Rahix/pavu-mixer/host-daemon/src/pa.rs

#![allow(unused_variables, dead_code)]

use crate::config;
use anyhow::Context;
use pulse::callbacks::ListResult;
use pulse::context;
use pulse::mainloop::standard as mainloop;
use std::cell::Cell;
use std::rc::Rc;
use std::sync::mpsc;

/// Sample Spec for monitoring streams
const SAMPLE_SPEC: pulse::sample::Spec = pulse::sample::Spec {
    format: pulse::sample::Format::FLOAT32NE,
    channels: 1,
    rate: 25,
};

pub struct SinkInputInfo {
    pub index: u32,
    pub name: Option<String>,
    pub application: Option<String>,
    connected_sink: u32,
    pub properties: pulse::proplist::Proplist,
    volume: pulse::volume::ChannelVolumes,
    mute: bool,
}

impl SinkInputInfo {
    fn from_pa(info: &context::introspect::SinkInputInfo) -> Self {
        Self {
            index: info.index,
            name: info.name.as_ref().map(|c| c.to_owned().into_owned()),
            application: info
                .proplist
                .get_str(pulse::proplist::properties::APPLICATION_NAME),
            connected_sink: info.sink,
            properties: info.proplist.clone(),
            volume: info.volume.clone(),
            mute: info.mute,
        }
    }
}

impl std::fmt::Debug for SinkInputInfo {
    fn fmt(&self, f: &mut std::fmt::Formatter<'_>) -> std::fmt::Result {
        let mut propmap = std::collections::BTreeMap::new();
        for key in self.properties.iter() {
            let value = self
                .properties
                .get_str(&key)
                .expect("missing property for iterated key");
            propmap.insert(key, value);
        }
        f.debug_struct("SinkInputInfo")
            .field("index", &self.index)
            .field("name", &self.name)
            .field("application", &self.application)
            .field("connected_sink", &self.connected_sink)
            .field("properties", &propmap)
            .field("volume", &self.volume.avg().print_verbose(true))
            .field("mute", &self.mute)
            .finish()
    }
}

pub struct SinkInfo {
    index: u32,
    name: Option<String>,
    monitoring_source: u32,
    volume: pulse::volume::ChannelVolumes,
    mute: bool,
}

impl SinkInfo {
    fn from_pa(info: &context::introspect::SinkInfo) -> Self {
        Self {
            index: info.index,
            name: info.name.as_ref().map(|c| c.to_owned().into_owned()),
            monitoring_source: info.monitor_source,
            volume: info.volume.clone(),
            mute: info.mute,
        }
    }
}

impl std::fmt::Debug for SinkInfo {
    fn fmt(&self, f: &mut std::fmt::Formatter<'_>) -> std::fmt::Result {
        f.debug_struct("SinkInfo")
            .field("index", &self.index)
            .field("name", &self.name)
            .field("monitoring_source", &self.monitoring_source)
            .field("volume", &self.volume.avg().print_verbose(true))
            .field("mute", &self.mute)
            .finish()
    }
}

#[derive(Debug)]
pub enum Event {
    /// After querying the default sink, PulseAudio came back with this stream.
    NewDefaultSink(Stream),
    /// A new sink-input showed up and we need to check whether it matches any of our channels - if
    /// yes, it should be attached.
    SinkInputAdded(SinkInputInfo),
    /// Some property of a sink-input changed.  It potentially needs to be re-attached to a
    /// different channel.
    SinkInputChanged(SinkInputInfo),
    /// A sink-input was removed and we should probably drop it from a potentially connected
    /// channel as well.
    SinkInputRemoved(u32),
    /// A new sink-input stream is available for the given channel.
    NewSinkInput(common::Channel, Stream),
    /// New signal peak information is available for this stream (sink / sink-input).
    NewPeakData(common::Channel, usize),
    // /// An error occurred asynchronously and we need to abort.
    // FatalError(anyhow::Error),
}

#[derive(Debug)]
enum InternalEvent {
    /// Sinks were added or removed (or default was changed) and we might need to reconnect the
    /// main channel.  This will trigger us to query the default sink next, leading to an external
    /// `DefaultSink` event.
    SinkUpdateNeeded,
    /// PulseAudio reported back the name of the default sink - we can now go and query its
    /// information.
    DefaultSinkName(String),
    /// We got information about the default sink - enough to create a stream for it.
    SinkData(SinkInfo),
    /// A new sink-input was detected - we should query its information and tell the application
    /// about it.
    SinkInputPending(u32),
    /// A sink-input change was detected - we should query its information and tell the application
    /// about the change.
    SinkInputChangePending(u32),
    /// We collected all relevant information for a new sink-input.
    RequestSinkInputStream {
        input_info: SinkInputInfo,
        for_channel: common::Channel,
        monitor_source: u32,
    },
}

/// Interface for interacting with Pulseaudio.
///
/// This interface will provide information about connect{ed,ing} streams, stream peak samples, and
/// allow the mixer to control stream volumes.
///
/// It is built upon the Pulseaudio single-threaded "simple" mainloop.
pub struct PulseInterface {
    mainloop: mainloop::Mainloop,
    pub context: context::Context,
    introspector: context::introspect::Introspector,
    external_rx: Option<mpsc::Receiver<Event>>,
    external_tx: mpsc::Sender<Event>,
    internal_rx: mpsc::Receiver<InternalEvent>,
    internal_tx: mpsc::Sender<InternalEvent>,

    /// Name of the current default sink (used to check if it changed).
    current_default_sink: Option<String>,
}

impl PulseInterface {
    pub fn init() -> anyhow::Result<Self> {
        let mut proplist = pulse::proplist::Proplist::new().context("failed creating proplist")?;
        proplist
            .set_str(
                pulse::proplist::properties::APPLICATION_NAME,
                "Pavu-Mixer Daemon",
            )
            .ok()
            .context("failed setting proplist string")?;

        let mut mainloop = mainloop::Mainloop::new().context("failed creating mainloop")?;
        let mut context =
            pulse::context::Context::new_with_proplist(&mainloop, "PavuMixerContext", &proplist)
                .context("failed creating context")?;
        context
            .connect(None, pulse::context::FlagSet::NOFLAGS, None)
            .context("failed connecting context")?;

        'wait_for_ctx: loop {
            Self::iterate_mainloop(&mut mainloop, true)?;
            match context.get_state() {
                pulse::context::State::Ready => {
                    break 'wait_for_ctx;
                }
                pulse::context::State::Terminated | pulse::context::State::Failed => {
                    anyhow::bail!("terminated or failed context");
                }
                _ => (),
            }
        }

        let introspector = context.introspect();

        let (external_tx, external_rx) = mpsc::channel();
        let (internal_tx, internal_rx) = mpsc::channel();

        context.set_subscribe_callback({
            let external_tx = external_tx.clone();
            let internal_tx = internal_tx.clone();
            Some(Box::new(move |facility, op, index| {
                use pulse::context::subscribe::Facility;
                use pulse::context::subscribe::Operation;

                // it would be very odd if PulseAudio gave us invalid enum values
                let op = op.expect("invalid subscribe callback params");
                let facility = facility.expect("invalid subscribe callback params");

                match (facility, op) {
                    (Facility::Sink, Operation::New) => internal_tx
                        .send(InternalEvent::SinkUpdateNeeded)
                        .expect("event channel error"),
                    (Facility::Sink, Operation::Removed) => internal_tx
                        .send(InternalEvent::SinkUpdateNeeded)
                        .expect("event channel error"),
                    (Facility::Sink, Operation::Changed) => (), // ignore
                    (Facility::Server, _) => internal_tx
                        .send(InternalEvent::SinkUpdateNeeded) // default sink might have changed
                        .expect("event channel error"),
                    (Facility::SinkInput, Operation::New) => internal_tx
                        .send(InternalEvent::SinkInputPending(index))
                        .expect("event channel error"),
                    (Facility::SinkInput, Operation::Removed) => external_tx
                        .send(Event::SinkInputRemoved(index))
                        .expect("event channel error"),
                    (Facility::SinkInput, Operation::Changed) => internal_tx
                        .send(InternalEvent::SinkInputChangePending(index))
                        .expect("event channel error"),
                    _ => unreachable!("unexpected facility: {:?}", facility),
                };
            }))
        });

        // subscribe to interesting events:
        // - SINK: if the available sinks (= output devices) change
        // - SINK_INPUT: if the playing audio sources change
        // - SERVER: if the selected default sink (output device) changes
        {
            use pulse::context::subscribe::InterestMaskSet;
            context.subscribe(
                InterestMaskSet::SINK | InterestMaskSet::SINK_INPUT | InterestMaskSet::SERVER,
                |_| (),
            );
        }

        // Queue initial events to get the mixer going.  This means triggering an update of the
        // default sink...
        internal_tx
            .send(InternalEvent::SinkUpdateNeeded)
            .expect("event channel error");

        // ...and "adding" all currently existing sink-inputs.
        let done = Rc::new(Cell::new(Ok(false)));
        introspector.get_sink_input_info_list({
            let external_tx = external_tx.clone();
            let done = done.clone();
            move |result| match result {
                ListResult::Item(info) => {
                    external_tx
                        .send(Event::SinkInputAdded(SinkInputInfo::from_pa(info)))
                        .expect("event channel error");
                }
                ListResult::Error => done.set(Err(anyhow::anyhow!("pulseaudio list error"))),
                ListResult::End => done.set(Ok(true)),
            }
        });

        let mut this = Self {
            mainloop,
            context,
            introspector,
            external_rx: Some(external_rx),
            external_tx,
            internal_rx,
            internal_tx,

            current_default_sink: None,
        };

        'add_all_sink_inputs: loop {
            this.iterate(true)?;
            // returns `true` once we hit the end of the sink-input list
            if done.replace(Ok(false))? {
                break 'add_all_sink_inputs;
            }
        }

        Ok(this)
    }

    fn iterate_mainloop(mainloop: &mut mainloop::Mainloop, block: bool) -> anyhow::Result<()> {
        match mainloop.iterate(block) {
            mainloop::IterateResult::Success(_) => Ok(()),
            mainloop::IterateResult::Quit(_) => unreachable!("no code should quit the mainloop!"),
            mainloop::IterateResult::Err(e) => Err(e).context("failed mainloop iteration"),
        }
    }

    pub fn take_event_receiver(&mut self) -> Option<mpsc::Receiver<Event>> {
        self.external_rx.take()
    }

    pub fn iterate(&mut self, block: bool) -> anyhow::Result<()> {
        Self::iterate_mainloop(&mut self.mainloop, block)?;
        while let Ok(event) = self.internal_rx.try_recv() {
            match event {
                InternalEvent::SinkUpdateNeeded => self.query_default_sink(),
                InternalEvent::DefaultSinkName(name) => {
                    if self.current_default_sink.as_ref() != Some(&name) {
                        // the name differs from the previous one - we need to issue an update
                        self.query_sink_data(&name);
                    }
                }
                InternalEvent::SinkData(info) => {
                    // Create a new stream and pass it to the application
                    let stream = Stream::new_for_sink(self, info)
                        .context("failed creating monitoring stream for default sink")?;
                    self.external_tx
                        .send(Event::NewDefaultSink(stream))
                        .expect("event channel error");
                }
                InternalEvent::SinkInputPending(index) => self.query_added_sink_input(index),
                InternalEvent::SinkInputChangePending(index) => {
                    self.query_changed_sink_input(index)
                }
                InternalEvent::RequestSinkInputStream {
                    input_info,
                    for_channel,
                    monitor_source,
                } => {
                    let stream = Stream::new_for_sink_input(self, input_info, monitor_source)?;
                    self.external_tx
                        .send(Event::NewSinkInput(for_channel, stream))
                        .expect("event channel error");
                }
            }
        }
        Ok(())
    }

    /// Request a stream for a sink-input.
    ///
    /// This will first query the sink-input's sink to get its monitoring source.
    ///
    /// Once received, the stream will be pushed as an event.
    pub fn request_sink_input_stream(
        &mut self,
        input_info: SinkInputInfo,
        for_channel: common::Channel,
    ) {
        let connected_sink = input_info.connected_sink;
        let mut input_info = Some(input_info);
        self.introspector.get_sink_info_by_index(connected_sink, {
            let internal_tx = self.internal_tx.clone();
            move |result| match result {
                ListResult::Item(info) => {
                    internal_tx
                        .send(InternalEvent::RequestSinkInputStream {
                            input_info: input_info.take().expect(
                                "callback for request_sink_input_stream() called too often",
                            ),
                            for_channel,
                            monitor_source: info.monitor_source,
                        })
                        .expect("event channel error");
                }
                ListResult::End => (),
                ListResult::Error => {
                    log::warn!("error while querying sink data - ignoring this sink")
                }
            }
        });
    }

    /// Query the default sink.
    ///
    /// Triggers [`InternalEvent::DefaultSinkName`] on completion.
    fn query_default_sink(&mut self) {
        self.introspector.get_server_info({
            let internal_tx = self.internal_tx.clone();
            move |info| {
                if let Some(default_sink) = &info.default_sink_name {
                    internal_tx.send(InternalEvent::DefaultSinkName(default_sink.clone().into_owned())).expect("event channel error");
                } else {
                    log::warn!("PulseAudio does not have a default sink - the main channel is not operational.");
                }
            }
        });
    }

    /// Query sink information for a sink.
    ///
    /// Triggers [`InternalEvent::SinkData`] on completion.
    fn query_sink_data(&mut self, sink_name: &str) {
        self.introspector.get_sink_info_by_name(sink_name, {
            let internal_tx = self.internal_tx.clone();
            move |result| match result {
                ListResult::Item(info) => {
                    internal_tx
                        .send(InternalEvent::SinkData(SinkInfo::from_pa(info)))
                        .expect("event channel error");
                }
                ListResult::End => (),
                ListResult::Error => {
                    log::warn!("error while querying sink data - ignoring this sink")
                }
            }
        });
    }

    /// Query a newly added sink-input.
    ///
    /// Triggers [`Event::SinkInputAdded`] on completion.
    fn query_added_sink_input(&mut self, index: u32) {
        self.introspector.get_sink_input_info(index, {
            let external_tx = self.external_tx.clone();
            move |result| match result {
                ListResult::Item(info) => {
                    external_tx
                        .send(Event::SinkInputAdded(SinkInputInfo::from_pa(info)))
                        .expect("event channel error");
                }
                ListResult::Error => {
                    log::debug!("Error while querying sink-input {} - ignoring.", index)
                }
                ListResult::End => (),
            }
        });
    }

    /// Query a changed sink-input.
    ///
    /// Triggers [`Event::SinkInputChanged`] on completion.
    fn query_changed_sink_input(&mut self, index: u32) {
        self.introspector.get_sink_input_info(index, {
            let external_tx = self.external_tx.clone();
            move |result| match result {
                ListResult::Item(info) => {
                    external_tx
                        .send(Event::SinkInputChanged(SinkInputInfo::from_pa(info)))
                        .expect("event channel error");
                }
                ListResult::Error => {
                    log::debug!("Error while querying sink-input {} - ignoring.", index)
                }
                ListResult::End => (),
            }
        });
    }
}

impl Drop for PulseInterface {
    fn drop(&mut self) {
        // SAFETY: Not doing this causes a segfault /o\
        self.context.disconnect();
    }
}

#[derive(Debug)]
enum StreamInfo {
    Sink(SinkInfo),
    SinkInput(SinkInputInfo),
}

impl StreamInfo {
    fn description(&self) -> String {
        match self {
            StreamInfo::Sink(s) => format!("Sink '{}'", s.name.as_deref().unwrap_or("unknown")),
            StreamInfo::SinkInput(s) => {
                format!("Sink-Input '{}'", s.name.as_deref().unwrap_or("unknown"))
            }
        }
    }

    fn volume(&mut self) -> &mut pulse::volume::ChannelVolumes {
        match self {
            StreamInfo::Sink(s) => &mut s.volume,
            StreamInfo::SinkInput(s) => &mut s.volume,
        }
    }

    fn muted(&self) -> bool {
        match self {
            StreamInfo::Sink(s) => s.mute,
            StreamInfo::SinkInput(s) => s.mute,
        }
    }
}

pub struct Stream {
    stream: pulse::stream::Stream,
    info: StreamInfo,
    connected_channel: Rc<Cell<Option<(common::Channel, usize)>>>,
    monitor_source: u32,
}

impl std::fmt::Debug for Stream {
    fn fmt(&self, f: &mut std::fmt::Formatter<'_>) -> std::fmt::Result {
        f.debug_struct("Stream").field("info", &self.info).finish()
    }
}

impl Stream {
    fn new_for_sink(pa: &mut PulseInterface, info: SinkInfo) -> anyhow::Result<Self> {
        let monitor_source = info.monitoring_source;
        Self::new(pa, StreamInfo::Sink(info), monitor_source)
    }

    fn new_for_sink_input(
        pa: &mut PulseInterface,
        info: SinkInputInfo,
        monitor_source: u32,
    ) -> anyhow::Result<Self> {
        Self::new(pa, StreamInfo::SinkInput(info), monitor_source)
    }

    fn new(pa: &mut PulseInterface, info: StreamInfo, monitor_source: u32) -> anyhow::Result<Self> {
        let mut stream = pulse::stream::Stream::new(
            &mut pa.context,
            &format!("Peak Detect for {}", info.description()),
            &SAMPLE_SPEC,
            None,
        )
        .context("failed creating monitoring stream")?;

        let connected_channel = Rc::new(Cell::new(None));

        stream.set_read_callback({
            let external_tx = pa.external_tx.clone();
            let connected_channel = connected_channel.clone();
            Some(Box::new(move |_length| {
                if let Some((ch, index)) = connected_channel.get() {
                    external_tx
                        .send(Event::NewPeakData(ch, index))
                        .expect("event channel error");
                }
            }))
        });

        if let StreamInfo::SinkInput(info) = &info {
            stream
                .set_monitor_stream(info.index)
                .context("failed setting sink-input monitor stream")?;
        }

        Ok(Self {
            stream,
            info,
            connected_channel,
            monitor_source,
        })
    }

    pub fn connect(&mut self) -> anyhow::Result<()> {
        // TODO: do DONT_INHIBIT_AUTO_SUSPEND and DONT_MOVE properly
        let mut flags =
            pulse::stream::FlagSet::PEAK_DETECT | pulse::stream::FlagSet::ADJUST_LATENCY;

        if let StreamInfo::SinkInput(_) = self.info {
            flags |= pulse::stream::FlagSet::DONT_MOVE;
        }

        let attrs = pulse::def::BufferAttr {
            fragsize: std::mem::size_of::<f32>() as u32,
            maxlength: u32::MAX,
            ..Default::default()
        };

        self.stream
            .connect_record(Some(&self.monitor_source.to_string()), Some(&attrs), flags)
            .context("failed connecting monitoring stream")?;

        Ok(())
    }

    pub fn set_connected_channel(&self, ch: common::Channel, index: usize) {
        self.connected_channel.set(Some((ch, index)));
    }

    pub fn is_for_sink_input(&self, sink_input: u32) -> bool {
        match &self.info {
            StreamInfo::Sink(_) => false,
            StreamInfo::SinkInput(info) => info.index == sink_input,
        }
    }

    pub fn sink_input_index(&self) -> Option<u32> {
        match &self.info {
            StreamInfo::Sink(_) => None,
            StreamInfo::SinkInput(info) => Some(info.index),
        }
    }

    pub fn get_recent_peak(&mut self) -> anyhow::Result<Option<f32>> {
        let mut recent_peak: Option<f32> = None;
        'peek_loop: loop {
            match self.stream.peek()? {
                pulse::stream::PeekResult::Empty => break 'peek_loop,
                pulse::stream::PeekResult::Hole(_) => {
                    self.stream.discard().context("failed dropping fragments")?;
                }
                pulse::stream::PeekResult::Data(buf) => {
                    use std::convert::TryInto;
                    let buf: [u8; 4] = buf.try_into().context("got fragment of wrong length")?;
                    let rp = recent_peak.get_or_insert(0.0);
                    *rp = rp.max(f32::from_ne_bytes(buf));
                    self.stream.discard().context("failed dropping fragments")?;
                }
            }
        }
        Ok(recent_peak)
    }

    pub fn set_volume(&mut self, pa: &mut PulseInterface, v: f32) {
        let pa_volume = pulse::volume::Volume((pulse::volume::Volume::NORMAL.0 as f32 * v) as u32);
        match &mut self.info {
            StreamInfo::Sink(SinkInfo { index, volume, .. }) => {
                volume.set(volume.len(), pa_volume);
                pa.introspector
                    .set_sink_volume_by_index(*index, volume, None);
            }
            StreamInfo::SinkInput(SinkInputInfo { index, volume, .. }) => {
                volume.set(volume.len(), pa_volume);
                pa.introspector.set_sink_input_volume(*index, volume, None);
            }
        }
    }

    pub fn set_mute(&mut self, pa: &mut PulseInterface, new_mute: bool) {
        match &mut self.info {
            StreamInfo::Sink(SinkInfo { index, mute, .. }) => {
                *mute = new_mute;
                pa.introspector.set_sink_mute_by_index(*index, *mute, None);
            }
            StreamInfo::SinkInput(SinkInputInfo { index, mute, .. }) => {
                *mute = new_mute;
                pa.introspector.set_sink_input_mute(*index, *mute, None);
            }
        }
    }

    pub fn is_mute(&self) -> bool {
        self.info.muted()
    }

    pub fn get_icon_name(&self, icon_mappings: &[config::IconMapping]) -> Option<String> {
        if let StreamInfo::SinkInput(info) = &self.info {
            'mappings_loop: for mapping in icon_mappings.iter() {
                for (name, value) in mapping.property_matches.iter() {
                    if info.properties.get_str(name).as_ref() != Some(value) {
                        continue 'mappings_loop;
                    }
                }
                return Some(mapping.icon.clone());
            }

            if let Some(icon) = info
                .properties
                .get_str(pulse::proplist::properties::APPLICATION_ICON_NAME)
            {
                return Some(icon);
            }
        }
        None
    }

    pub fn sink_name(&self) -> Option<String> {
        if let StreamInfo::Sink(info) = &self.info {
            info.name.clone()
        } else {
            None
        }
    }
}

impl Drop for Stream {
    fn drop(&mut self) {
        if self.stream.get_state() != pulse::stream::State::Unconnected {
            self.stream.set_read_callback(None);
            // explicitly ignore disconnection errors - we don't care!
            let _ = self.stream.disconnect();
        }
    }
}
